ChromeBee/Hall-Effect-Sensor-CAD-Mouse-Spacemouse/Springs/STLs/smaller TPU hook/TPU Spring 0.6x17mm V2.stl

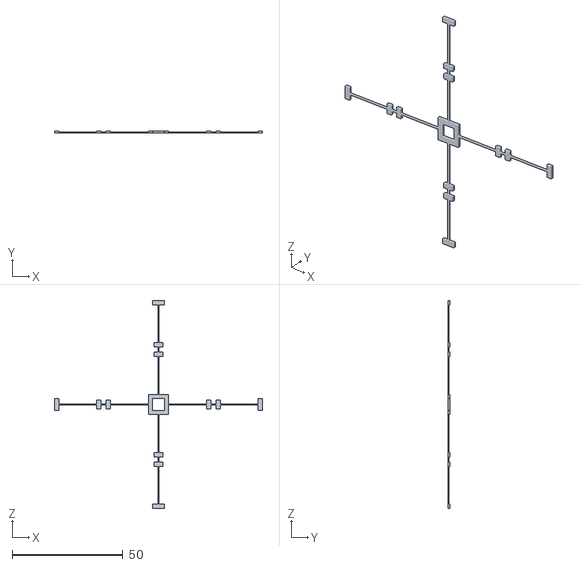
[picture p16: CAD file, 2024-11-24]
Springs/STLs/smaller TPU hook/TPU Spring 0.6x17mm V2.stl
93.8 x 1.00 x 93.8
