ChromeBee/Hall-Effect-Sensor-CAD-Mouse-Spacemouse/Springs/Wave_Spring_Experiment/lower mount.stl

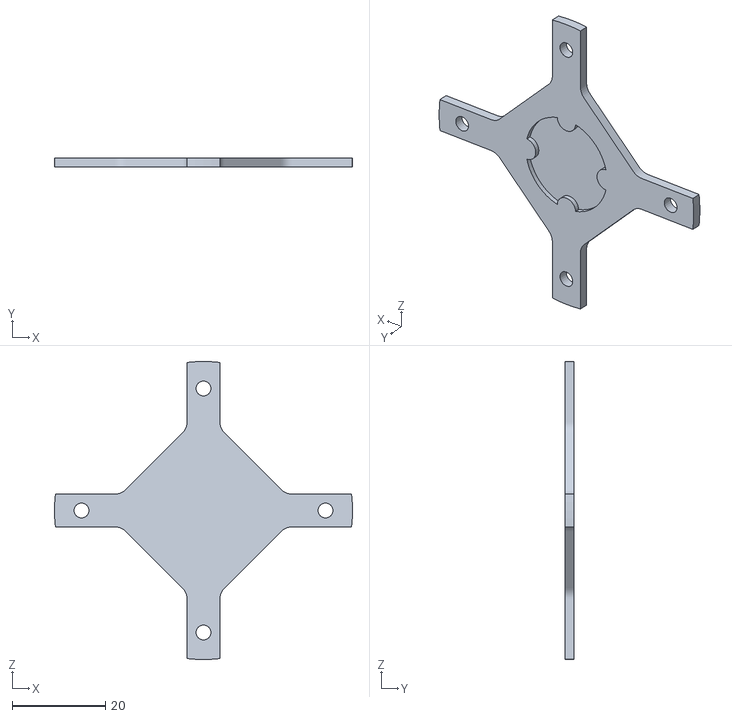
[picture p17: CAD file, 2025-08-18]
Springs/Wave_Spring_Experiment/lower mount.stl
64.0 x 2.00 x 64.0
