ChromeBee/Hall-Effect-Sensor-CAD-Mouse-Spacemouse/STL Files/Wire Hook.stl

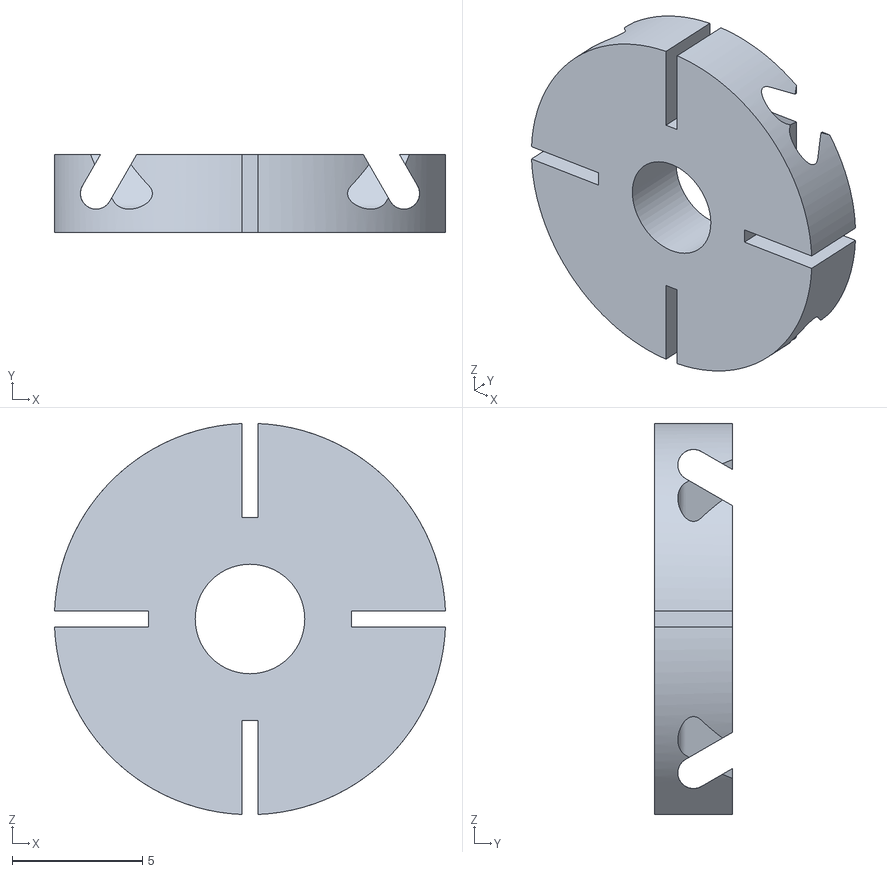
[picture p18: CAD file, 2024-07-11]
STL Files/Wire Hook.stl
15.0 x 3.00 x 15.0
