ChromeBee/Hall-Effect-Sensor-CAD-Mouse-Spacemouse/Smaller Case/Spacemouse knob flush magnet plate.stl

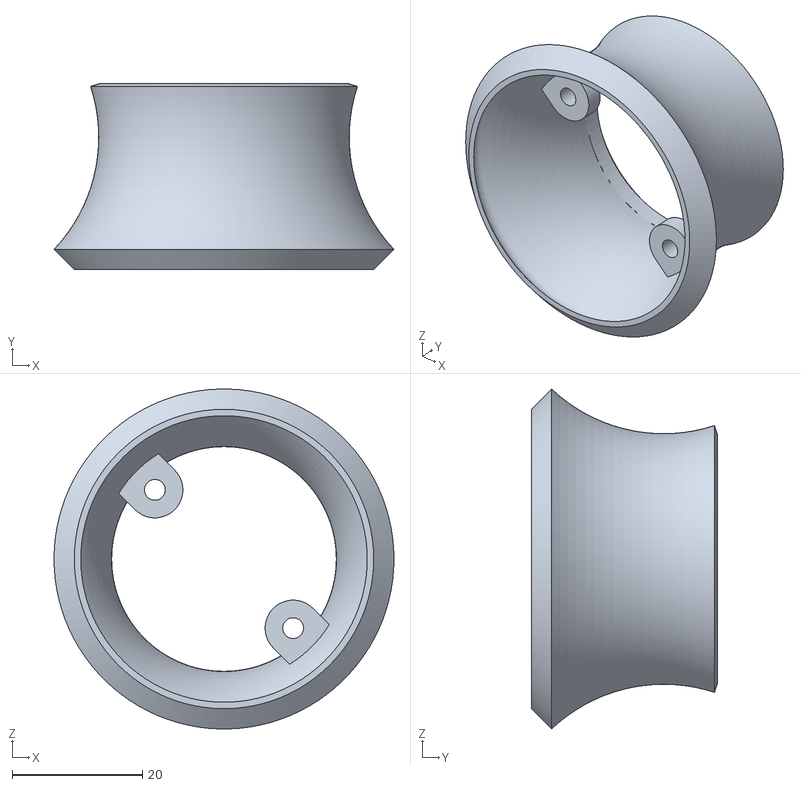
[picture p19: CAD file, 2025-02-06]
Smaller Case/Spacemouse knob flush magnet plate.stl
52.2 x 28.6 x 52.1
