ChromeBee/Hall-Effect-Sensor-CAD-Mouse-Spacemouse/Springs/STLs/smaller TPU hook/TPU Spring 0.6x18mm v2.stl

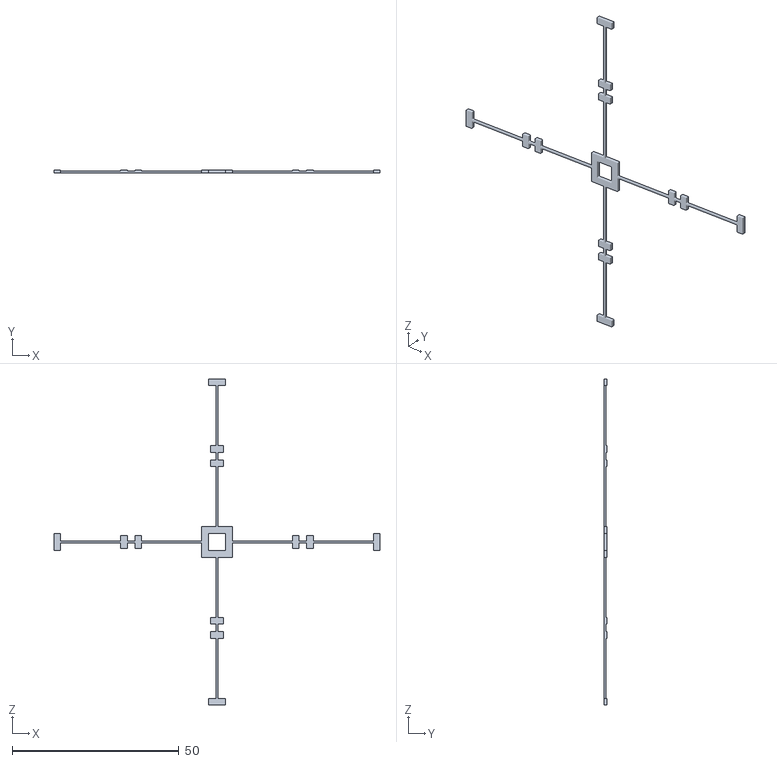
[picture p20: CAD file, 2024-11-24]
Springs/STLs/smaller TPU hook/TPU Spring 0.6x18mm v2.stl
97.8 x 1.00 x 97.8
