ChromeBee/Hall-Effect-Sensor-CAD-Mouse-Spacemouse/Springs/Wave_Spring_Experiment/Spacemouse knob Wave spring (smaller case).stl

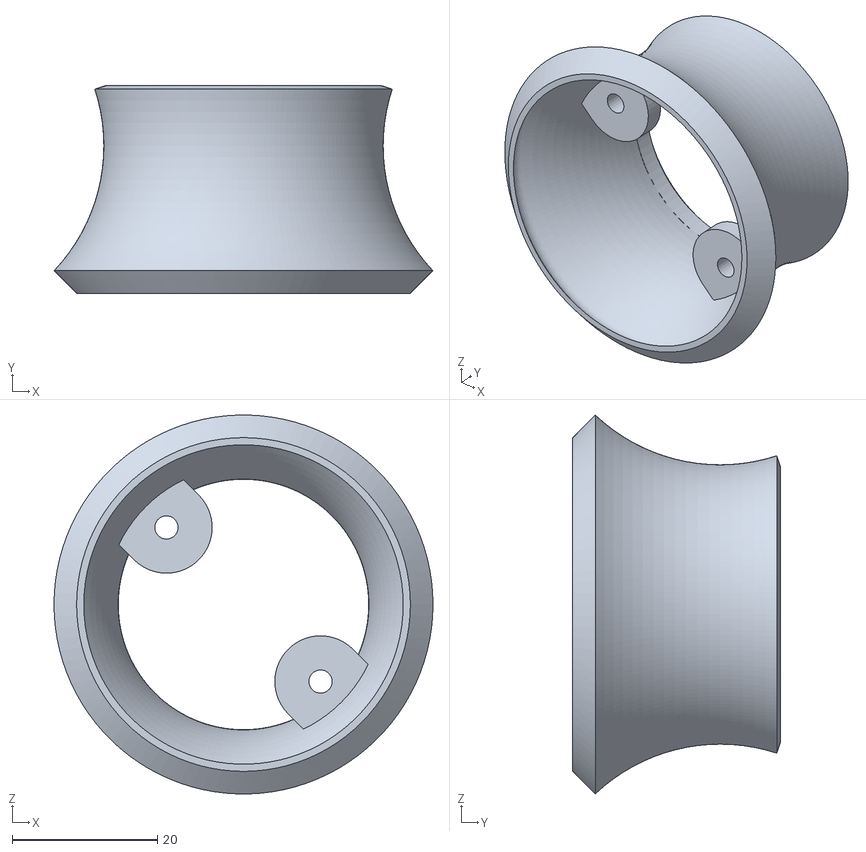
[picture p22: CAD file, 2025-08-14]
Springs/Wave_Spring_Experiment/Spacemouse knob Wave spring (smaller case).stl
52.2 x 28.6 x 52.1
