ChromeBee/Hall-Effect-Sensor-CAD-Mouse-Spacemouse/STL Files/Button.stl

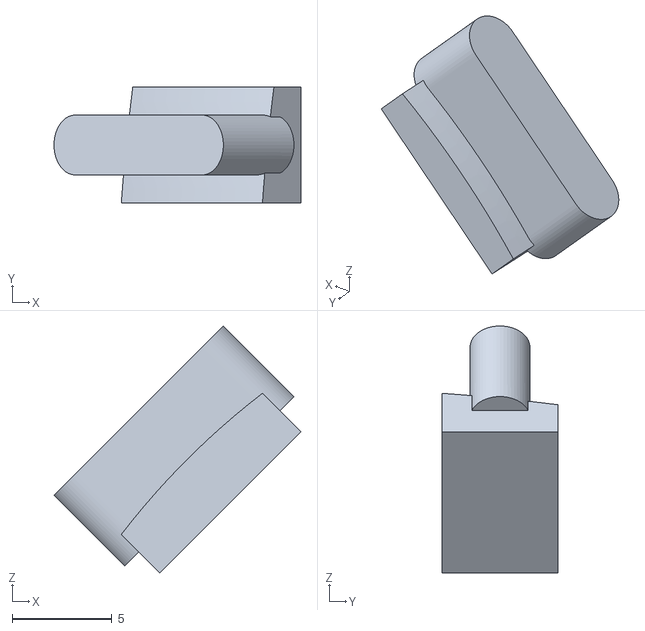
[picture p23: CAD file, 2024-07-11]
STL Files/Button.stl
12.4 x 5.80 x 12.4
