ChromeBee/Hall-Effect-Sensor-CAD-Mouse-Spacemouse/Smaller Case/Button v3 (extended -smaller case).stl

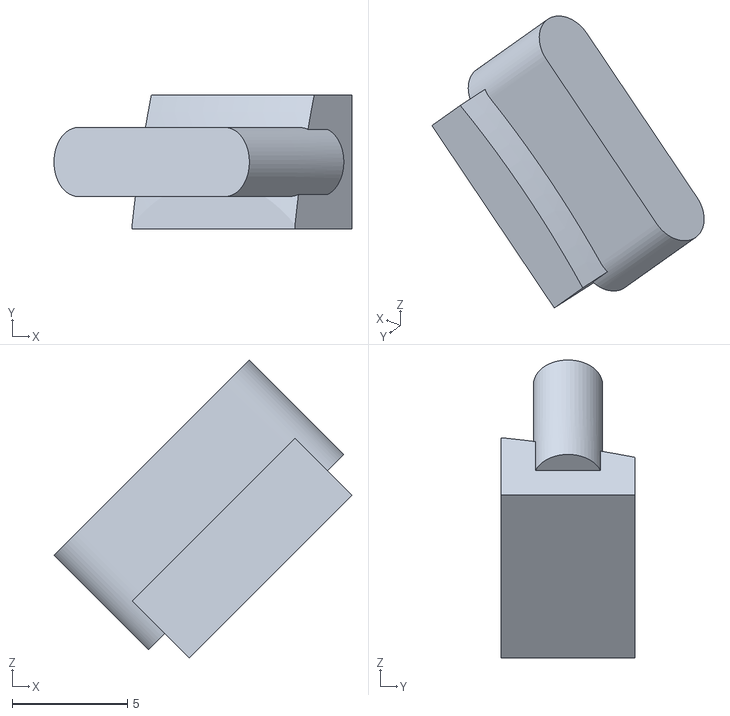
[picture p24: CAD file, 2025-02-06]
Smaller Case/Button v3 (extended -smaller case).stl
12.9 x 5.80 x 12.9
