ChromeBee/Hall-Effect-Sensor-CAD-Mouse-Spacemouse/Springs/Wave_Spring_Experiment/upper mount side 1.stl

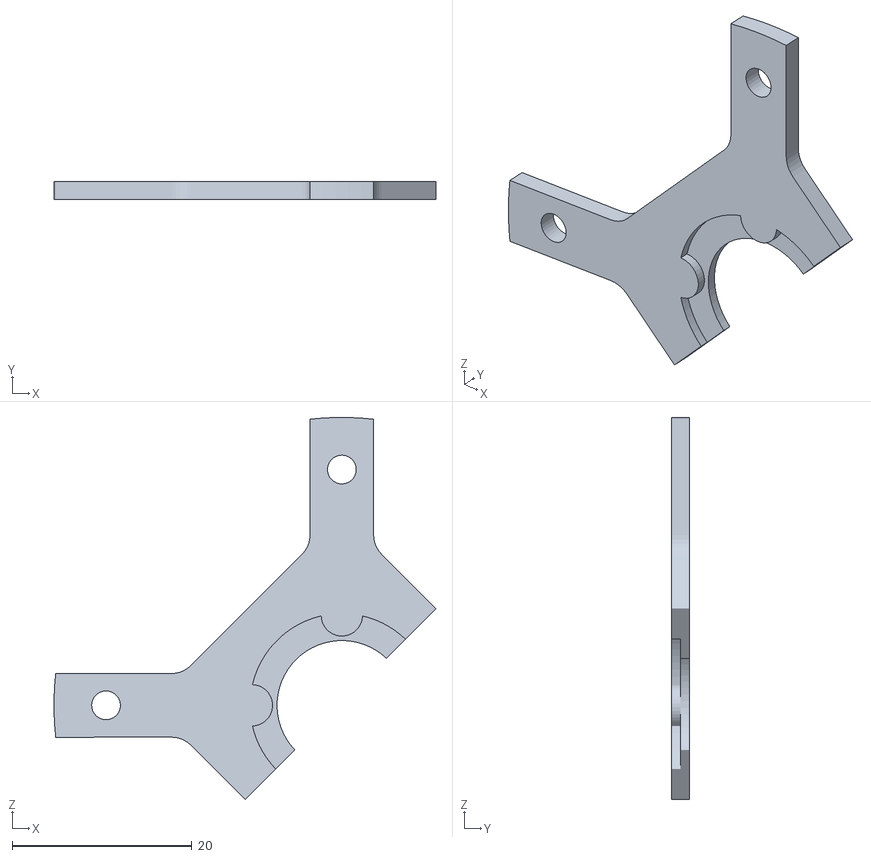
[picture p26: CAD file, 2025-08-14]
Springs/Wave_Spring_Experiment/upper mount side 1.stl
42.5 x 2.00 x 42.5
