ChromeBee/Hall-Effect-Sensor-CAD-Mouse-Spacemouse/STL Files/Spacemouse knob cap.stl

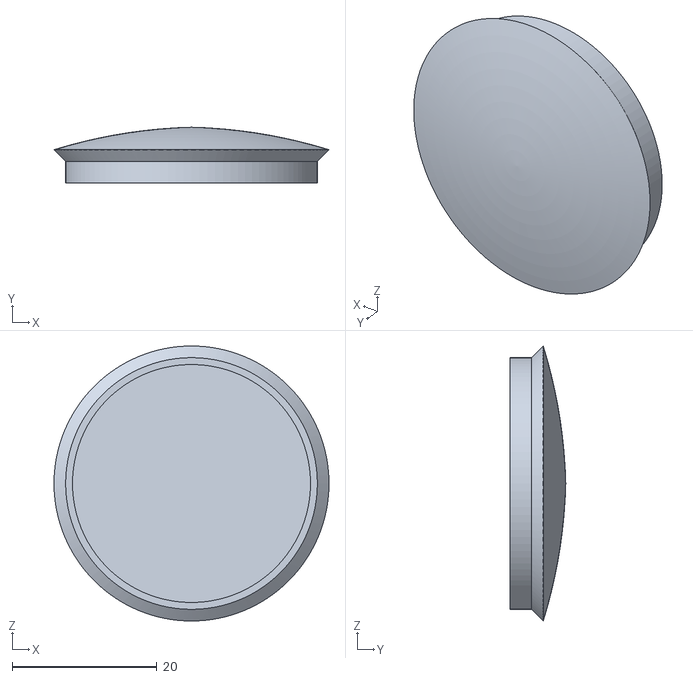
[picture p27: CAD file, 2024-07-11]
STL Files/Spacemouse knob cap.stl
38.0 x 7.68 x 38.0
