ChromeBee/Hall-Effect-Sensor-CAD-Mouse-Spacemouse/Springs/STLs/TPU Spring 0.1x15mm.stl

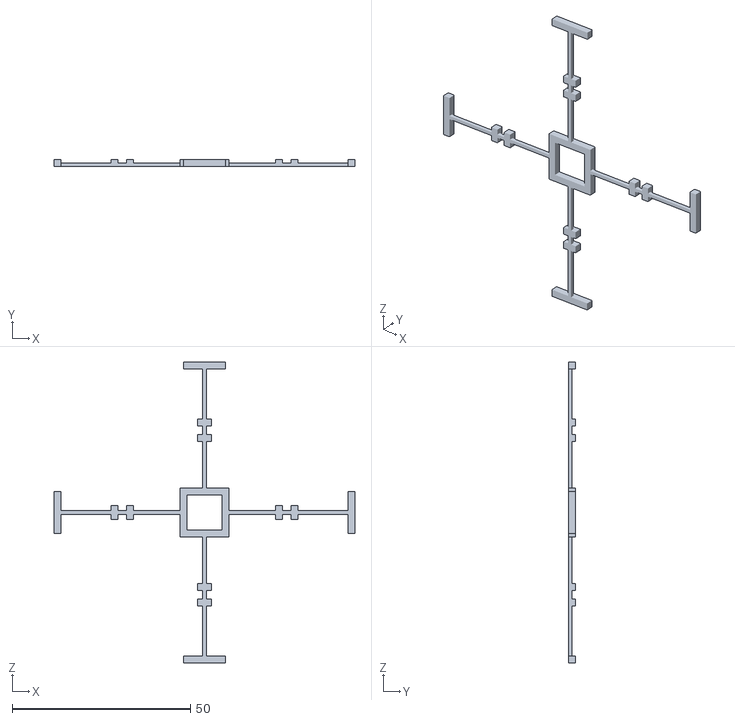
[picture p28: CAD file, 2024-08-01]
Springs/STLs/TPU Spring 0.1x15mm.stl
84.4 x 2.00 x 84.4
