ChromeBee/Hall-Effect-Sensor-CAD-Mouse-Spacemouse/STL Files/magnet plate.stl

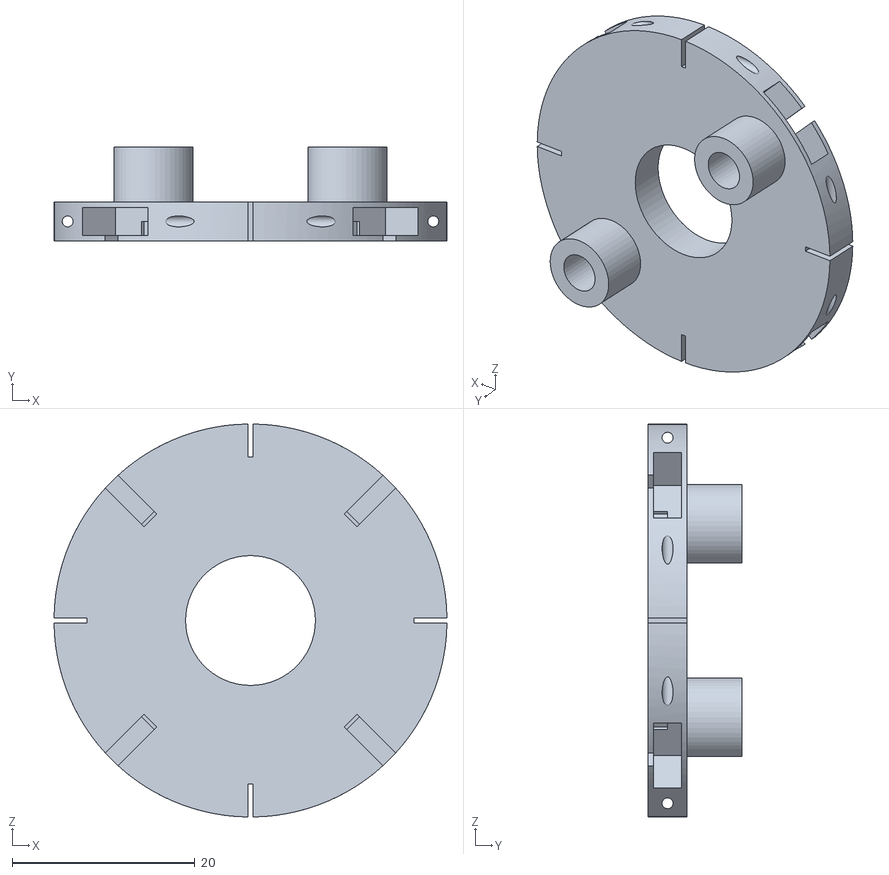
[picture p29: CAD file, 2024-07-11]
STL Files/magnet plate.stl
43.0 x 10.3 x 43.0
