ChromeBee/Hall-Effect-Sensor-CAD-Mouse-Spacemouse/Springs/STLs/TPU Hook.stl

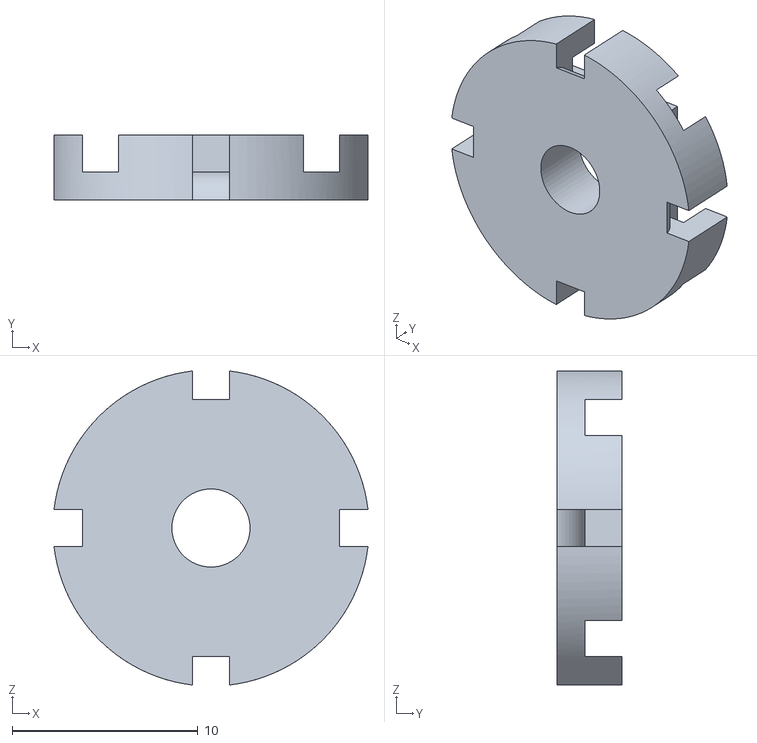
[picture p30: CAD file, 2024-08-01]
Springs/STLs/TPU Hook.stl
16.9 x 3.50 x 16.9
