ChromeBee/Hall-Effect-Sensor-CAD-Mouse-Spacemouse/Springs/Wave_Spring_Experiment/Hall Effect Spacemouse smaller V3.step

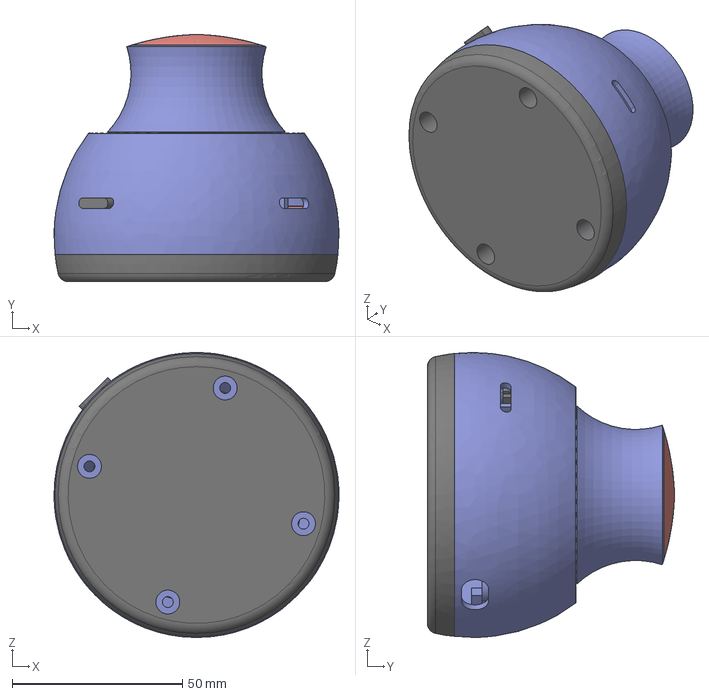
[picture p31: CAD file, 2025-04-08]
Springs/Wave_Spring_Experiment/Hall Effect Spacemouse smaller V3.step
83.6 x 72.5 x 83.6 mm
