ChromeBee/Hall-Effect-Sensor-CAD-Mouse-Spacemouse/STL Files/sensor plate.stl

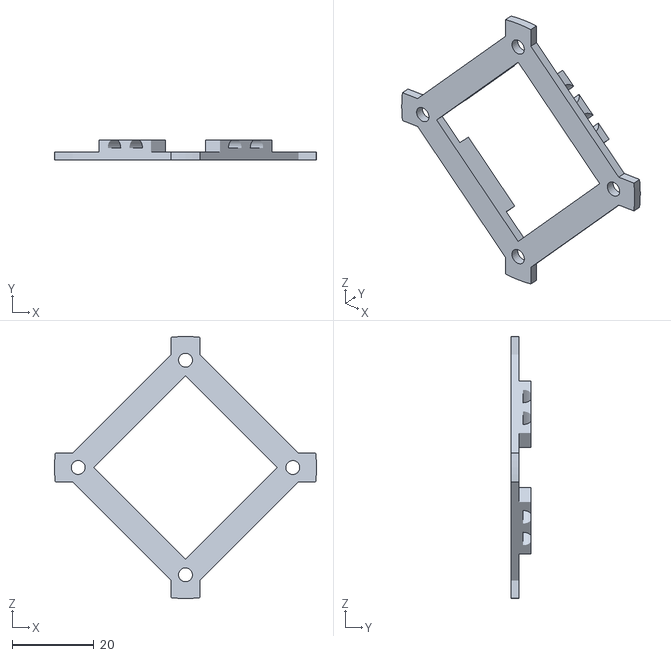
[picture p32: CAD file, 2024-07-11]
STL Files/sensor plate.stl
64.0 x 5.00 x 64.0
