ChromeBee/Hall-Effect-Sensor-CAD-Mouse-Spacemouse/STL Files/Base.stl

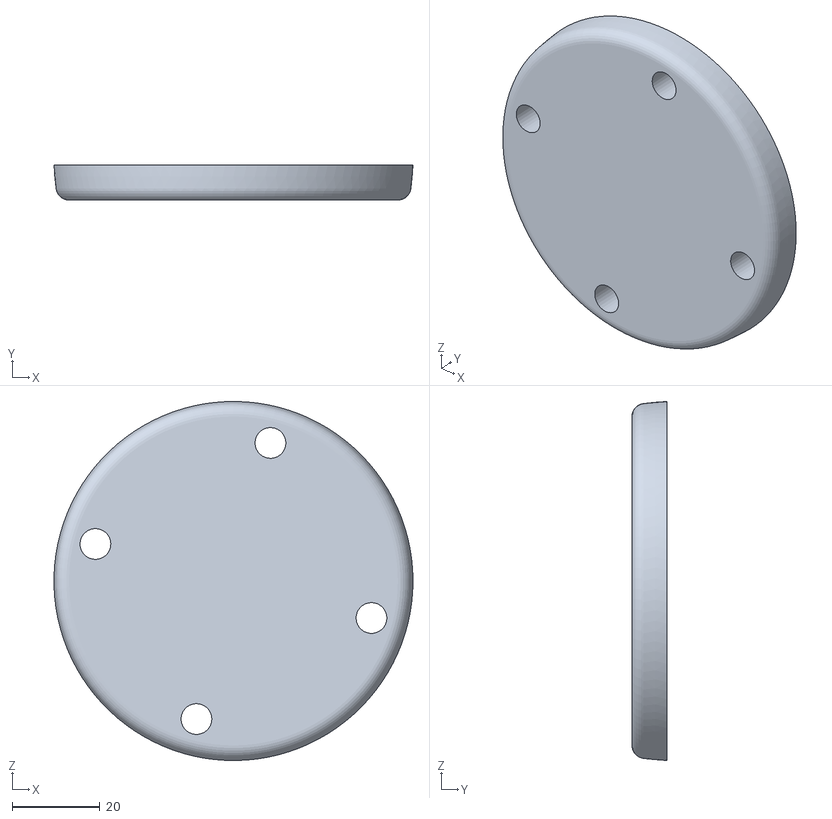
[picture p33: CAD file, 2024-07-11]
STL Files/Base.stl
81.7 x 8.00 x 81.7
