ChromeBee/Hall-Effect-Sensor-CAD-Mouse-Spacemouse/STL Files/Arduino Plate.stl

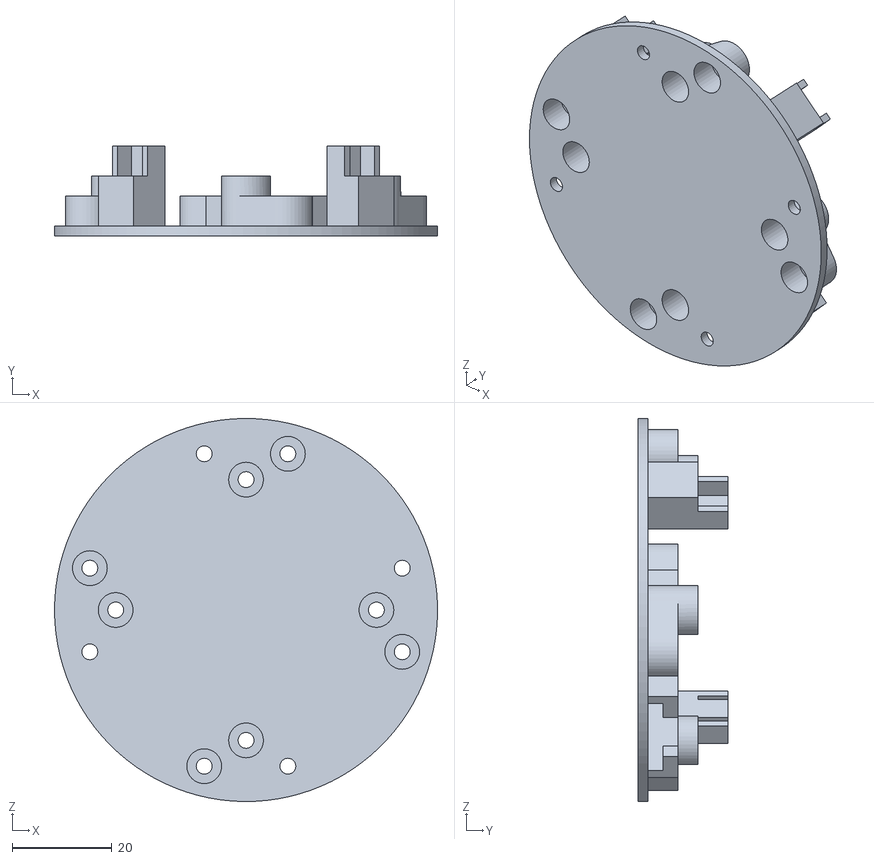
[picture p34: CAD file, 2024-07-11]
STL Files/Arduino Plate.stl
77.0 x 18.0 x 77.0
