ChromeBee/Hall-Effect-Sensor-CAD-Mouse-Spacemouse/STL Files/Case.stl

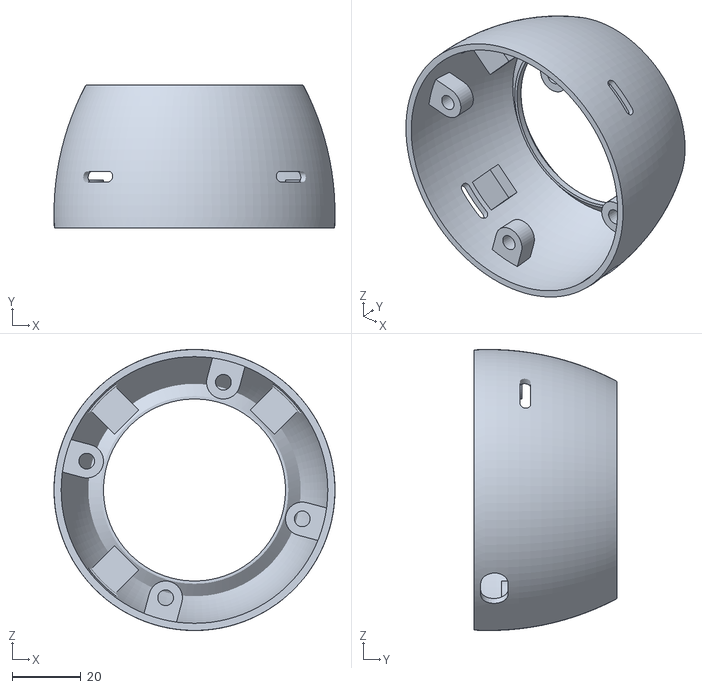
[picture p35: CAD file, 2024-07-11]
STL Files/Case.stl
81.8 x 41.8 x 81.9
