ChromeBee/Hall-Effect-Sensor-CAD-Mouse-Spacemouse/STL Files/Spacemouse knob.stl

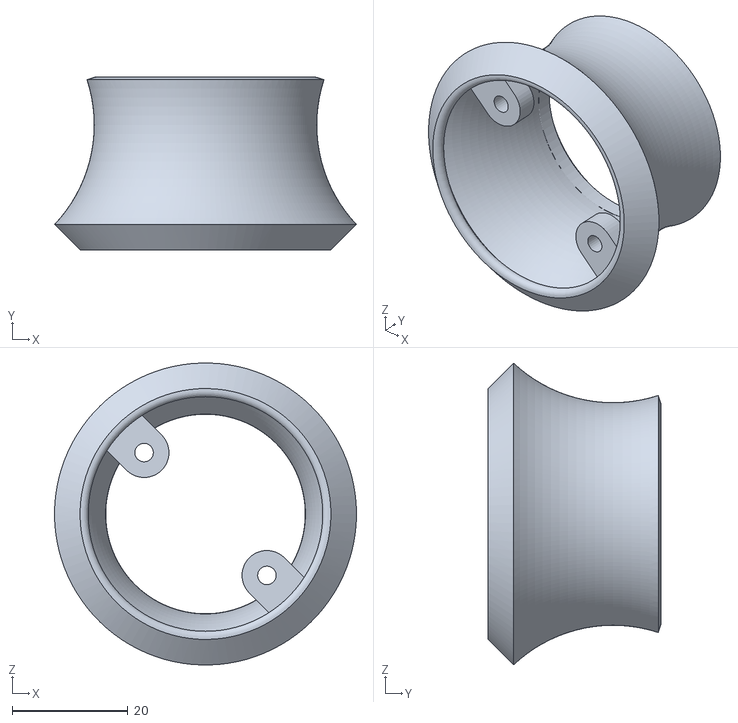
[picture p36: CAD file, 2024-07-11]
STL Files/Spacemouse knob.stl
52.2 x 29.9 x 52.1
